MisterHW/CSI2-SPY-22/CSI2-SPY-22-1A/output/RevA_layers.png

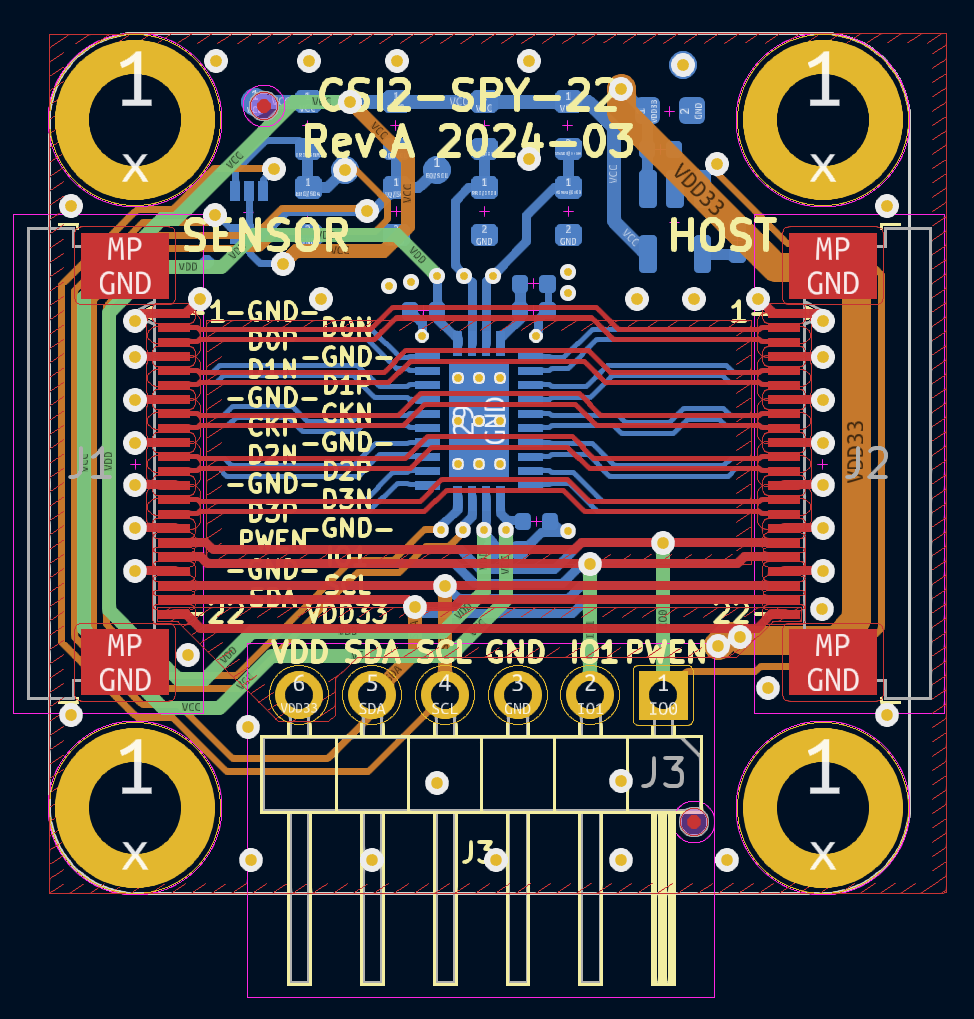
CSI2-SPY-22-1A/output/RevA_layers.png
